shy-neon/vfdRevival/IMG_0012.jpg

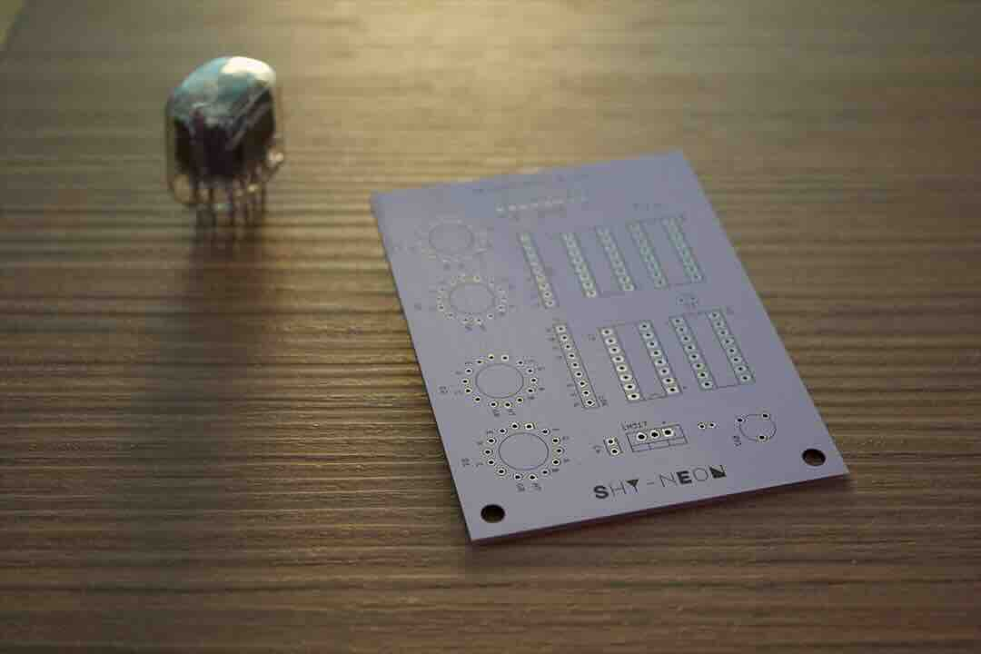
IMG_0012.jpg
